stevenchadburrow/AcolyteHandheld/HandheldPIC32.kicad_sch

## KiCad design HandheldPIC32.kicad_sch (2025-06-16)

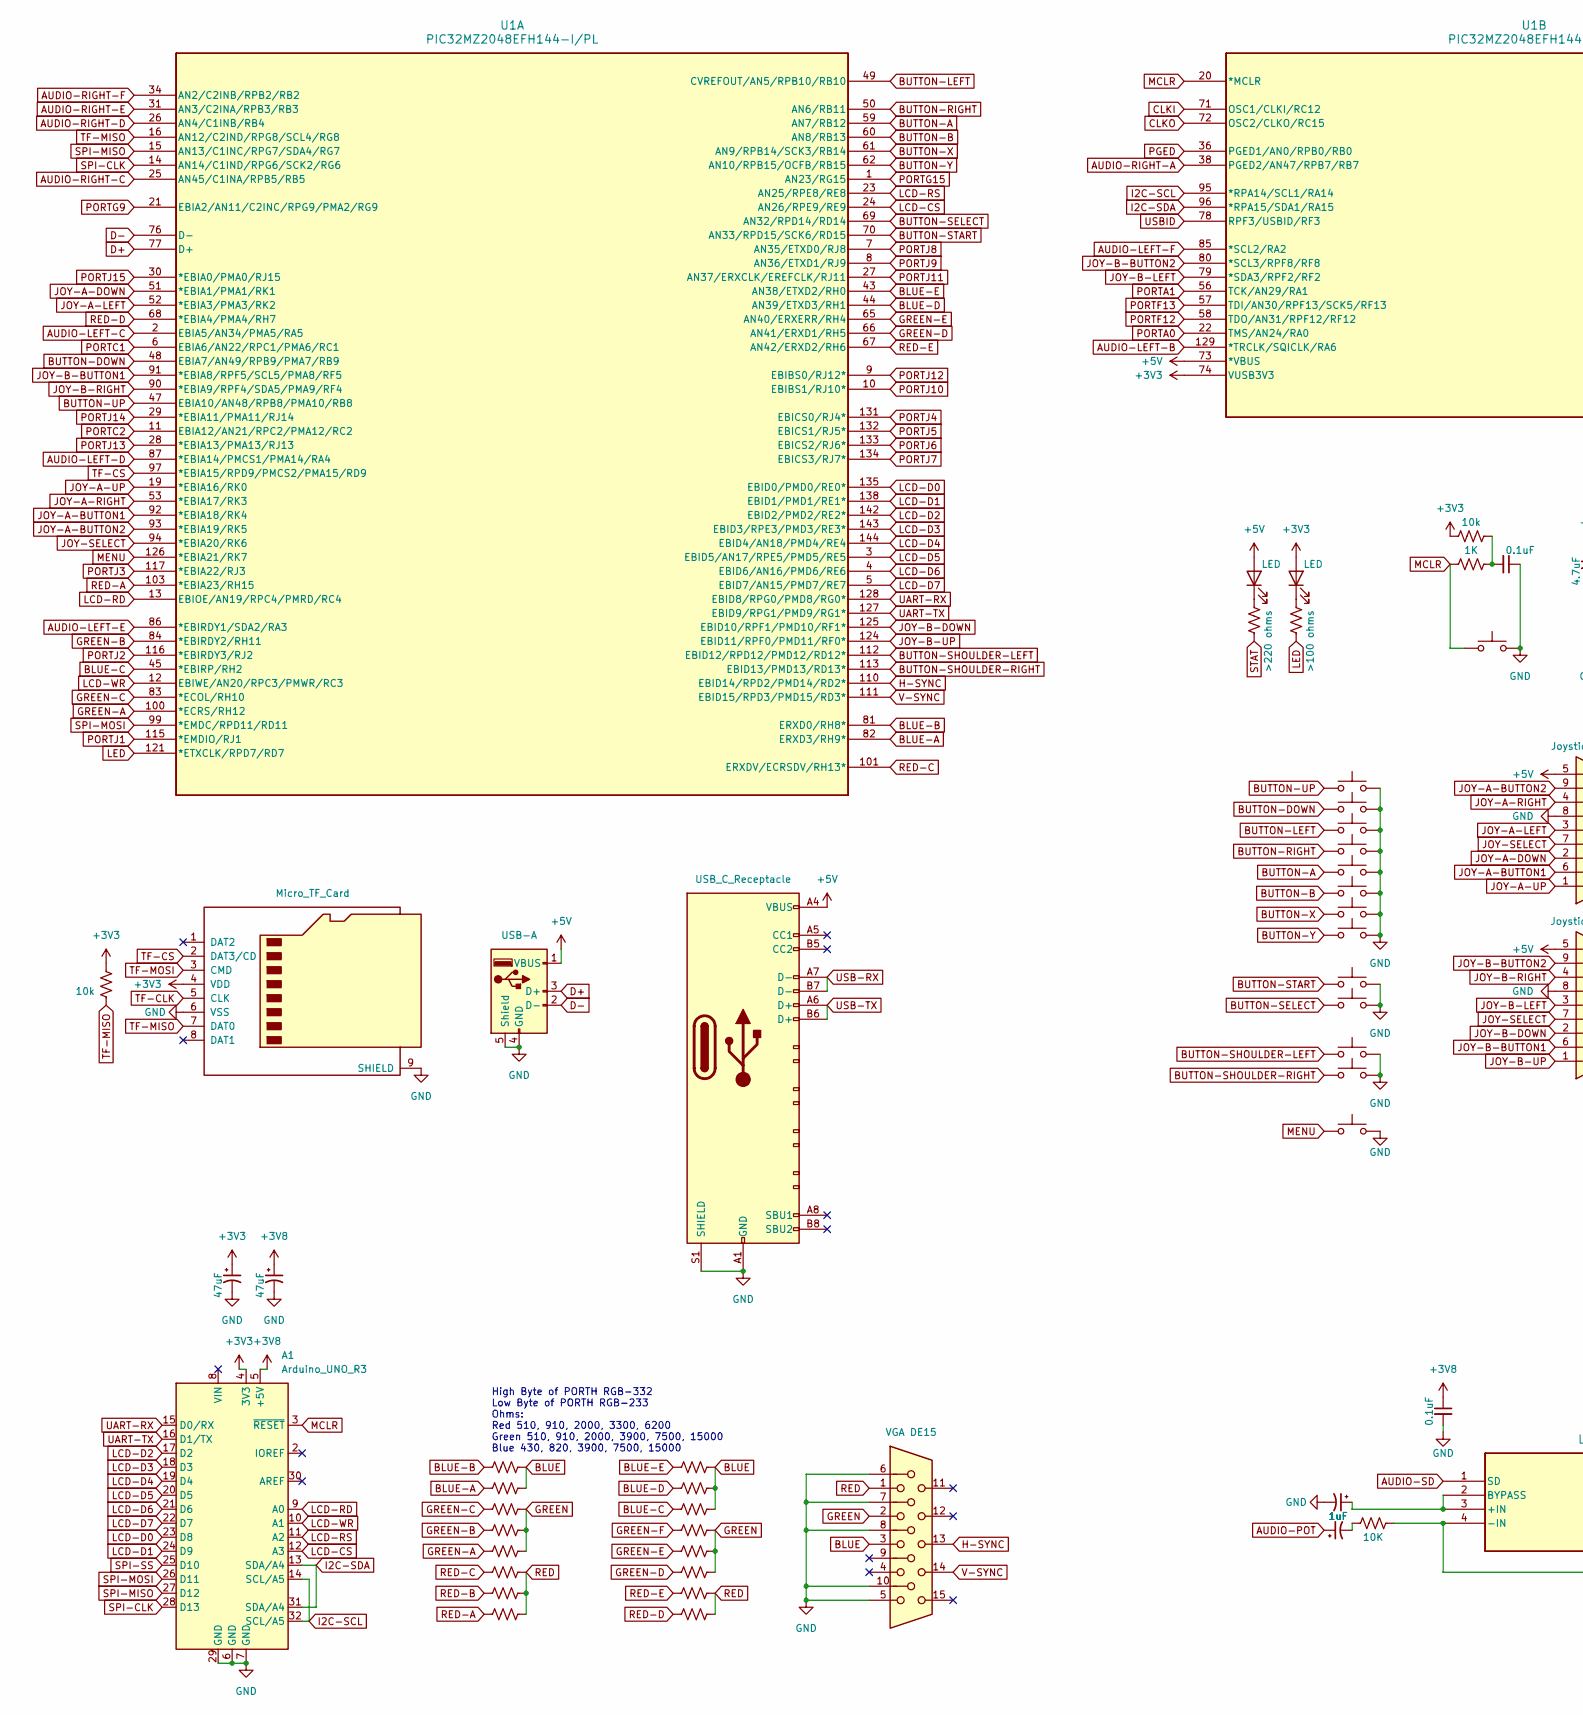
[picture p9: schematic HandheldPIC32.kicad_sch, part in row 1, column 1]

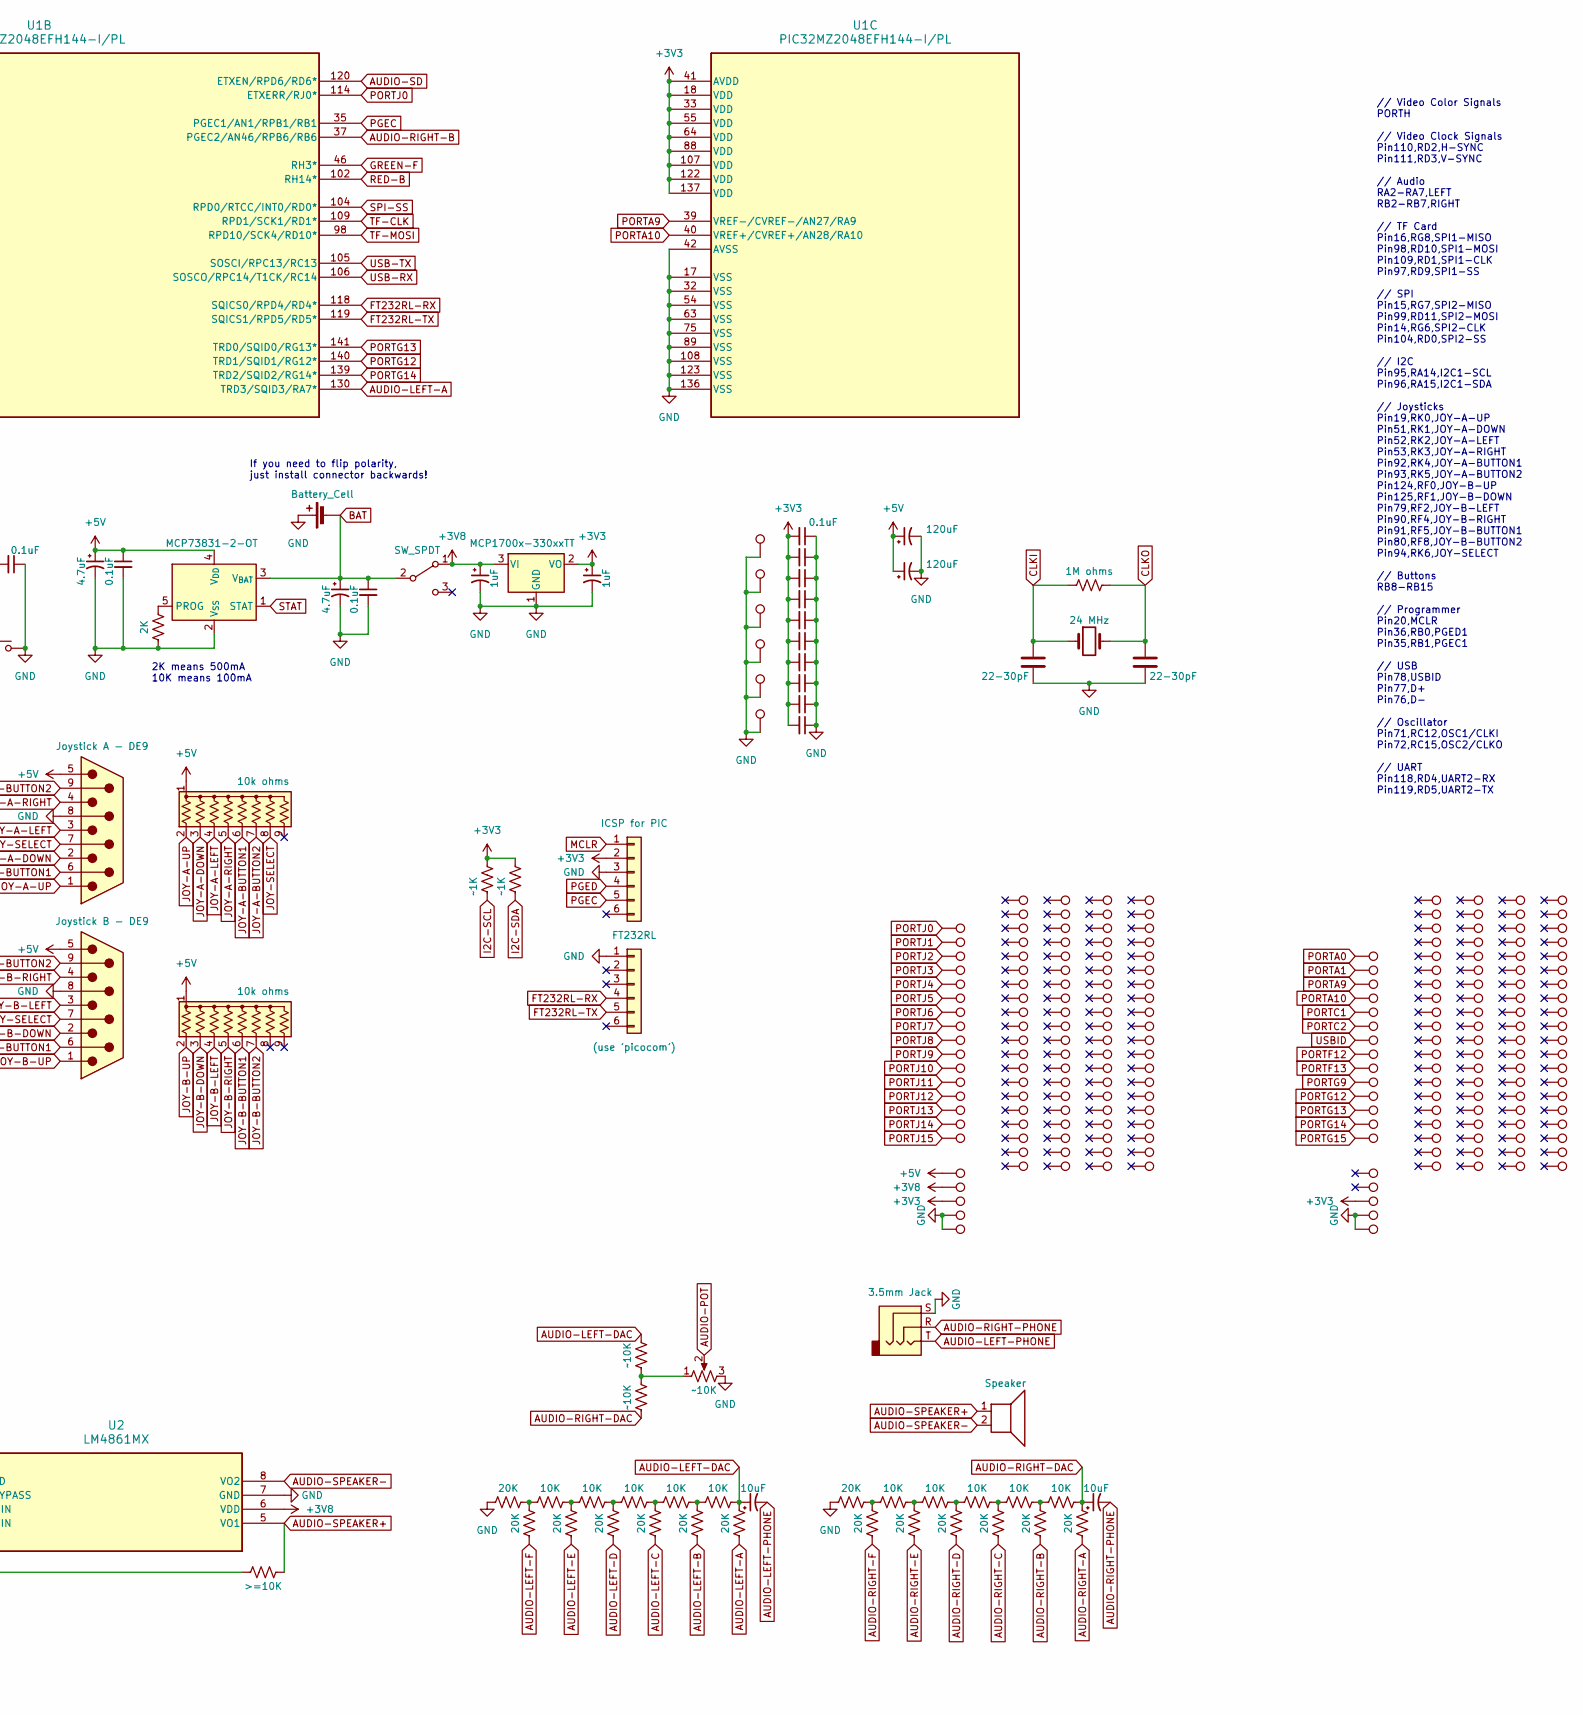
[picture p10: schematic HandheldPIC32.kicad_sch, part in row 1, column 2]

Parts:
A1: Arduino_UNO_R3; Arduino_UNO_R3-modified
BT1: Battery_Cell; JST_PH_B2B-PH-K_1x02_P2.00mm_Vertical
C1, C18, C19, C21, C22, C23, C24, C25, C26, C27: C_Polarized_Small_US; CP_Radial_D6.3mm_P2.50mm
C2, C3: C; C_Disc_D3.8mm_W2.6mm_P2.50mm
C4, C5, C6, C7, C8, C9, C10, C11, C12, C13, C14, C15, C20, C33: C_Small; C_Disc_D3.0mm_W1.6mm_P2.50mm
C16, C17: C_Polarized_Small_US; CP_Radial_D8.0mm_P3.50mm
D1, D3: LED; CustomLED
J1: DE15_Receptacle_HighDensity; DSUB-15-HD_Female_Horizontal_P2.29x2.54mm_VGA
J2: Conn_01x06; PinHeader_1x06_P2.54mm_Horizontal
J3: Conn_01x06; PinSocket_1x06_P2.54mm_Horizontal
J4: AudioJack3; BIGJack_3.5mm_Ledino_KB3SPRS_Horizontal
J6: USB_A; USB_A_Molex_67643_Horizontal
J8, J9: DE9_Plug; DSUB-9_Male_Horizontal_P2.77x2.84mm_EdgePinOffset7.70mm_Hou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
J10: USB_C_Receptacle; USB_C_Receptacle_GCT_USB4085
J11: Micro_TF_Card; microSD_HC_Hirose_DM3D-SF
LS1: Speaker; JST_PH_B2B-PH-K_1x02_P2.00mm_Vertical
R1, R2, R3, R4, R5, R6, R7, R8, R9, R10, R11, R12, R13, R14, R15, R16, R17, R18, R19, R20, R21, R22, R23, R24, R25, R26, R27, R28, R29, R30, R31, R32, R33, R34, R35, R36, R37, R38, R39, R40, R41, R42, R43, R44, R45, R46, R47, R48, R49, R50, R51, R53, R54: R_US; R_Axial_DIN0207_L6.3mm_D2.5mm_P10.16mm_Horizontal
RN1, RN2: R_Network08_US; R_Array_SIP9
RV1: R_Potentiometer_US; Potentiometer_Bourns_PTV09A-2_Single_Horizontal
SW1, SW2, SW3, SW5, SW6, SW7, SW8, SW9, SW10, SW11, SW12, SW15: SW_Push; SW_PUSH_6mm_H8mm
SW4: SW_SPDT; SW_E-Switch_EG1224_SPDT_Angled
SW14, SW16: SW_Push; SW_Tactile_SPST_Angled_PTS645Vx83-2LFS
TP1, TP2, TP3, TP4, TP6, TP7: TestPoint; ScrewHole-4-40
TP5, TP8, TP9, TP10, TP11, TP12, TP18, TP19, TP20, TP21, TP22, TP23, TP24, TP25, TP26, TP27, TP28, TP29, TP30, TP31, TP32, TP33, TP34, TP35, TP36, TP37, TP38, TP39, TP40, TP41, TP42, TP43, TP44, TP45, TP46, TP47, TP48, TP49, TP50, TP51, TP52, TP53, TP54, TP55, TP56, TP57, TP58, TP59, TP60, TP61, TP62, TP63, TP64, TP65, TP66, TP67, TP68, TP69, TP70, TP71, TP72, TP73, TP74, TP75, TP76, TP77, TP78, TP79, TP80, TP81, TP82, TP83, TP84, TP85, TP86, TP87, TP117, TP118, TP119, TP120, TP121, TP122, TP123, TP124, TP125, TP126, TP127, TP128, TP129, TP130, TP131, TP132, TP133, TP134, TP135, TP136, TP137, TP138, TP139, TP140, TP141, TP142, TP143, TP144, TP145, TP146, TP147, TP148, TP149, TP150, TP151, TP152, TP153, TP154, TP155, TP156, TP157, TP158, TP159, TP160, TP161, TP162, TP163, TP164, TP165, TP166, TP167, TP168, TP169, TP170, TP171, TP172, TP173, TP174, TP175, TP176, TP177, TP178, TP179, TP180, TP181, TP182, TP183, TP184, TP185, TP186, TP187, TP188, TP189, TP190, TP191, TP192, TP193, TP194, TP195, TP196, TP197, TP198, TP199, TP200, TP201, TP202, TP203, TP204, TP205, TP206, TP207, TP208, TP209, TP210: TestPoint; TestPointStdTHT
TP13, TP14, TP15, TP16, TP17, TP88, TP89, TP90, TP91, TP92, TP93, TP94, TP95, TP96, TP97, TP98, TP99, TP100, TP101, TP102, TP103, TP104, TP105, TP106, TP107, TP108, TP109, TP110, TP111, TP112: TestPoint; TestPoint_custom_THTPad_D1.5mm_Drill0.7mm
U1: PIC32MZ2048EFH144-I/PL; LQFP144_PL_MCH
U2: LM4861MX; SOIC-8_3.9x4.9mm_P1.27mm
U3: MCP73831-2-OT; SOT-23-5
U4: MCP1700x-330xxTT; SOT-23
Y1: Crystal; Crystal_HC49-4H_Vertical

Connections:
+3V3: A1.4 (3V3), C6.2, C7.2, C8.2, C9.2, C10.2, C11.2, C12.2, C13.2, C14.2, C15.2, C22.1, C23.1, D1.2 (A), J2.2, J11.4 (VDD), R21.2, R22.2, R35.1, R38.1, TP10.1, TP119.1, U1.18 (VDD), U1.33 (VDD), U1.41 (AVDD), U1.55 (VDD), U1.64 (VDD), U1.74 (VUSB3V3), U1.88 (VDD), U1.107 (VDD), U1.122 (VDD), U1.137 (VDD), U4.2 (VO)
+3V8: A1.5 (+5V), C1.1, C24.1, C33.1, SW4.1 (A), TP9.1, U2.6 (VDD), U4.3 (VI)
+5V: C16.1, C17.1, C20.1, C26.1, D3.2 (A), J6.1 (VBUS), J8.5, J9.5, J10.A4 (VBUS), J10.A9 (VBUS), J10.B4 (VBUS), J10.B9 (VBUS), RN1.1 (common), RN2.1 (common), TP8.1, U1.73 (*VBUS), U3.4 (V_{DD})
AUDIO-LEFT-A: R37.2, U1.130 (TRD3/SQID3/RA7*)
AUDIO-LEFT-B: R23.2, U1.129 (*TRCLK/SQICLK/RA6)
AUDIO-LEFT-C: R26.2, U1.2 (EBIA5/AN34/PMA5/RA5)
AUDIO-LEFT-D: R28.2, U1.87 (*EBIA14/PMCS1/PMA14/RA4)
AUDIO-LEFT-DAC: C21.1, R34.1, R37.1, R50.1
AUDIO-LEFT-E: R31.2, U1.86 (*EBIRDY1/SDA2/RA3)
AUDIO-LEFT-F: R32.2, U1.85 (*SCL2/RA2)
AUDIO-LEFT-PHONE: C21.2, J4.T
AUDIO-POT: C19.1, RV1.2
AUDIO-RIGHT-A: R49.2, U1.38 (PGED2/AN47/RPB7/RB7)
AUDIO-RIGHT-B: R47.2, U1.37 (PGEC2/AN46/RPB6/RB6)
AUDIO-RIGHT-C: R45.2, U1.25 (AN45/C1INA/RPB5/RB5)
AUDIO-RIGHT-D: R43.2, U1.26 (AN4/C1INB/RB4)
AUDIO-RIGHT-DAC: C27.1, R48.1, R49.1, R51.2
AUDIO-RIGHT-E: R41.2, U1.31 (AN3/C2INA/RPB3/RB3)
AUDIO-RIGHT-F: R39.2, U1.34 (AN2/C2INB/RPB2/RB2)
AUDIO-RIGHT-PHONE: C27.2, J4.R
AUDIO-SD: U1.120 (ETXEN/RPD6/RD6*), U2.1 (SD)
AUDIO-SPEAKER+: LS1.1, R54.2, U2.5 (VO1)
AUDIO-SPEAKER-: LS1.2, U2.8 (VO2)
BAT: BT1.2 (-), C4.1, C25.1, SW4.2 (B), U3.3 (V_{BAT})
BLUE: J1.3, R1.1, R2.1, R10.1, R11.1, R12.1
BLUE-A: R2.2, U1.82 (ERXD3/RH9*)
BLUE-B: R1.2, U1.81 (ERXD0/RH8*)
BLUE-C: R12.2, U1.45 (*EBIRP/RH2)
BLUE-D: R11.2, U1.44 (AN39/ETXD3/RH1)
BLUE-E: R10.2, U1.43 (AN38/ETXD2/RH0)
BUTTON-A: SW8.1, U1.59 (AN7/RB12)
BUTTON-B: SW9.1, U1.60 (AN8/RB13)
BUTTON-DOWN: SW5.1, U1.48 (EBIA7/AN49/RPB9/PMA7/RB9)
BUTTON-LEFT: SW6.1, U1.49 (CVREFOUT/AN5/RPB10/RB10)
BUTTON-RIGHT: SW7.1, U1.50 (AN6/RB11)
BUTTON-SELECT: SW2.1, U1.69 (AN32/RPD14/RD14)
BUTTON-SHOULDER-LEFT: SW14.1, U1.112 (EBID12/RPD12/PMD12/RD12*)
BUTTON-SHOULDER-RIGHT: SW16.1, U1.113 (EBID13/PMD13/RD13*)
BUTTON-START: SW1.1, U1.70 (AN33/RPD15/SCK6/RD15)
BUTTON-UP: SW3.1, U1.47 (EBIA10/AN48/RPB8/PMA10/RB8)
BUTTON-X: SW10.1, U1.61 (AN9/RPB14/SCK3/RB14)
BUTTON-Y: SW11.1, U1.62 (AN10/RPB15/OCFB/RB15)
CLKI: C2.1, R9.1, U1.71 (OSC1/CLKI/RC12), Y1.1
CLKO: C3.1, R9.2, U1.72 (OSC2/CLKO/RC15), Y1.2
D+: J6.3 (D+), U1.77 (D+)
D-: J6.2 (D-), U1.76 (D-)
FT232RL-RX: J3.4, U1.118 (SQICS0/RPD4/RD4*)
FT232RL-TX: J3.5, U1.119 (SQICS1/RPD5/RD5*)
GND: A1.6 (GND), A1.7 (GND), A1.29 (GND), BT1.1 (+), C1.2, C2.2, C3.2, C4.2, C5.1, C6.1, C7.1, C8.1, C9.1, C10.1, C11.1, C12.1, C13.1, C14.1, C15.1, C16.2, C17.2, C18.2, C20.2, C22.2, C23.2, C24.2, C25.2, C26.2, C33.2, J1.5, J1.6, J1.7, J1.8, J1.10, J2.3, J3.1, J4.S, J6.4 (GND), J6.5 (Shield), J8.8, J9.8, J10.A1 (GND), J10.A12 (GND), J10.B1 (GND), J10.B12 (GND), J10.S1 (SHIELD), J11.6 (VSS), J11.9 (SHIELD), R20.2, R30.2, R33.2, RV1.3, SW1.2, SW2.2, SW3.2, SW5.2, SW6.2, SW7.2, SW8.2, SW9.2, SW10.2, SW11.2, SW12.2, SW14.2, SW15.2, SW16.2, TP1.1, TP2.1, TP3.1, TP4.1, TP6.1, TP7.1, TP11.1, TP12.1, TP120.1, TP121.1, U1.17 (VSS), U1.32 (VSS), U1.42 (AVSS), U1.54 (VSS), U1.63 (VSS), U1.75 (VSS), U1.89 (VSS), U1.108 (VSS), U1.123 (VSS), U1.136 (VSS), U2.7 (GND), U3.2 (V_{SS}), U4.1 (GND)
GREEN: J1.2, R3.1, R4.1, R5.1, R13.1, R14.1, R15.1
GREEN-A: R5.2, U1.100 (*ECRS/RH12)
GREEN-B: R4.2, U1.84 (*EBIRDY2/RH11)
GREEN-C: R3.2, U1.83 (*ECOL/RH10)
GREEN-D: R15.2, U1.66 (AN41/ERXD1/RH5)
GREEN-E: R14.2, U1.65 (AN40/ERXERR/RH4)
GREEN-F: R13.2, U1.46 (RH3*)
H-SYNC: J1.13, U1.110 (EBID14/RPD2/PMD14/RD2*)
I2C-SCL: A1.14 (SCL/A5), A1.32 (SCL/A5), R35.2, U1.95 (*RPA14/SCL1/RA14)
I2C-SDA: A1.13 (SDA/A4), A1.31 (SDA/A4), R38.2, U1.96 (*RPA15/SDA1/RA15)
JOY-A-BUTTON1: J8.6, RN1.6 (R5), U1.92 (*EBIA18/RK4)
JOY-A-BUTTON2: J8.9, RN1.7 (R6), U1.93 (*EBIA19/RK5)
JOY-A-DOWN: J8.2, RN1.3 (R2), U1.51 (*EBIA1/PMA1/RK1)
JOY-A-LEFT: J8.3, RN1.4 (R3), U1.52 (*EBIA3/PMA3/RK2)
JOY-A-RIGHT: J8.4, RN1.5 (R4), U1.53 (*EBIA17/RK3)
JOY-A-UP: J8.1, RN1.2 (R1), U1.19 (*EBIA16/RK0)
JOY-B-BUTTON1: J9.6, RN2.6 (R5), U1.91 (*EBIA8/RPF5/SCL5/PMA8/RF5)
JOY-B-BUTTON2: J9.9, RN2.7 (R6), U1.80 (*SCL3/RPF8/RF8)
JOY-B-DOWN: J9.2, RN2.3 (R2), U1.125 (EBID10/RPF1/PMD10/RF1*)
JOY-B-LEFT: J9.3, RN2.4 (R3), U1.79 (*SDA3/RPF2/RF2)
JOY-B-RIGHT: J9.4, RN2.5 (R4), U1.90 (*EBIA9/RPF4/SDA5/PMA9/RF4)
JOY-B-UP: J9.1, RN2.2 (R1), U1.124 (EBID11/RPF0/PMD11/RF0*)
JOY-SELECT: J8.7, J9.7, RN1.8 (R7), U1.94 (*EBIA20/RK6)
LCD-CS: A1.12 (A3), U1.24 (AN26/RPE9/RE9)
LCD-D0: A1.23 (D8), U1.135 (EBID0/PMD0/RE0*)
LCD-D1: A1.24 (D9), U1.138 (EBID1/PMD1/RE1*)
LCD-D2: A1.17 (D2), U1.142 (EBID2/PMD2/RE2*)
LCD-D3: A1.18 (D3), U1.143 (EBID3/RPE3/PMD3/RE3*)
LCD-D4: A1.19 (D4), U1.144 (EBID4/AN18/PMD4/RE4)
LCD-D5: A1.20 (D5), U1.3 (EBID5/AN17/RPE5/PMD5/RE5)
LCD-D6: A1.21 (D6), U1.4 (EBID6/AN16/PMD6/RE6)
LCD-D7: A1.22 (D7), U1.5 (EBID7/AN15/PMD7/RE7)
LCD-RD: A1.9 (A0), U1.13 (EBIOE/AN19/RPC4/PMRD/RC4)
LCD-RS: A1.11 (A2), U1.23 (AN25/RPE8/RE8)
LCD-WR: A1.10 (A1), U1.12 (EBIWE/AN20/RPC3/PMWR/RC3)
LED: R25.2, U1.121 (*ETXCLK/RPD7/RD7)
MCLR: A1.3 (~RESET), J2.1, R18.2, SW15.1, U1.20 (*MCLR)
MENU: SW12.1, U1.126 (*EBIA21/RK7)
unnamed: C5.2, R18.1, R21.1
unnamed: C18.1, U2.2 (BYPASS), U2.3 (+IN)
unnamed: C19.2, R53.1
unnamed: D1.1 (K), R25.1
unnamed: D3.1 (K), R36.1
unnamed: R19.1, R24.2, R31.1
unnamed: R19.2, R32.1, R33.1
unnamed: R20.1, U3.5 (PROG)
unnamed: R23.1, R29.1, R34.2
unnamed: R24.1, R27.2, R28.1
unnamed: R26.1, R27.1, R29.2
unnamed: R30.1, R39.1, R40.2
unnamed: R40.1, R41.1, R42.2
unnamed: R42.1, R43.1, R44.2
unnamed: R44.1, R45.1, R46.2
unnamed: R46.1, R47.1, R48.2
unnamed: R50.2, R51.1, RV1.1
unnamed: R53.2, R54.1, U2.4 (-IN)
PGEC: J2.5, U1.35 (PGEC1/AN1/RPB1/RB1)
PGED: J2.4, U1.36 (PGED1/AN0/RPB0/RB0)
PORTA0: TP14.1, U1.22 (TMS/AN24/RA0)
PORTA1: TP13.1, U1.56 (TCK/AN29/RA1)
PORTA9: TP15.1, U1.39 (VREF-/CVREF-/AN27/RA9)
PORTA10: TP16.1, U1.40 (VREF+/CVREF+/AN28/RA10)
PORTC1: TP17.1, U1.6 (EBIA6/AN22/RPC1/PMA6/RC1)
PORTC2: TP88.1, U1.11 (EBIA12/AN21/RPC2/PMA12/RC2)
PORTF12: TP90.1, U1.58 (TDO/AN31/RPF12/RF12)
PORTF13: TP91.1, U1.57 (TDI/AN30/RPF13/SCK5/RF13)
PORTG9: TP108.1, U1.21 (EBIA2/AN11/C2INC/RPG9/PMA2/RG9)
PORTG12: TP109.1, U1.140 (TRD1/SQID1/RG12*)
PORTG13: TP110.1, U1.141 (TRD0/SQID0/RG13*)
PORTG14: TP111.1, U1.139 (TRD2/SQID2/RG14*)
PORTG15: TP112.1, U1.1 (AN23/RG15)
PORTJ0: TP92.1, U1.114 (ETXERR/RJ0*)
PORTJ1: TP93.1, U1.115 (*EMDIO/RJ1)
PORTJ2: TP94.1, U1.116 (*EBIRDY3/RJ2)
PORTJ3: TP95.1, U1.117 (*EBIA22/RJ3)
PORTJ4: TP96.1, U1.131 (EBICS0/RJ4*)
PORTJ5: TP97.1, U1.132 (EBICS1/RJ5*)
PORTJ6: TP98.1, U1.133 (EBICS2/RJ6*)
PORTJ7: TP99.1, U1.134 (EBICS3/RJ7*)
PORTJ8: TP100.1, U1.7 (AN35/ETXD0/RJ8)
PORTJ9: TP101.1, U1.8 (AN36/ETXD1/RJ9)
PORTJ10: TP102.1, U1.10 (EBIBS1/RJ10*)
PORTJ11: TP103.1, U1.27 (AN37/ERXCLK/EREFCLK/RJ11)
PORTJ12: TP104.1, U1.9 (EBIBS0/RJ12*)
PORTJ13: TP105.1, U1.28 (*EBIA13/PMA13/RJ13)
PORTJ14: TP106.1, U1.29 (*EBIA11/PMA11/RJ14)
PORTJ15: TP107.1, U1.30 (*EBIA0/PMA0/RJ15)
RED: J1.1, R6.1, R7.1, R8.1, R16.1, R17.1
RED-A: R8.2, U1.103 (*EBIA23/RH15)
RED-B: R7.2, U1.102 (RH14*)
RED-C: R6.2, U1.101 (ERXDV/ECRSDV/RH13*)
RED-D: R17.2, U1.68 (*EBIA4/PMA4/RH7)
RED-E: R16.2, U1.67 (AN42/ERXD2/RH6)
SPI-CLK: A1.28 (D13), U1.14 (AN14/C1IND/RPG6/SCK2/RG6)
SPI-MISO: A1.27 (D12), U1.15 (AN13/C1INC/RPG7/SDA4/RG7)
SPI-MOSI: A1.26 (D11), U1.99 (*EMDC/RPD11/RD11)
SPI-SS: A1.25 (D10), U1.104 (RPD0/RTCC/INT0/RD0*)
STAT: R36.2, U3.1 (STAT)
TF-CLK: J11.5 (CLK), U1.109 (RPD1/SCK1/RD1*)
TF-CS: J11.2 (DAT3/CD), U1.97 (*EBIA15/RPD9/PMCS2/PMA15/RD9)
TF-MISO: J11.7 (DAT0), R22.1, U1.16 (AN12/C2IND/RPG8/SCL4/RG8)
TF-MOSI: J11.3 (CMD), U1.98 (RPD10/SCK4/RD10*)
UART-RX: A1.15 (D0/RX), U1.128 (EBID8/RPG0/PMD8/RG0*)
UART-TX: A1.16 (D1/TX), U1.127 (EBID9/RPG1/PMD9/RG1*)
USB-RX: J10.A7 (D-), J10.B7 (D-), U1.106 (SOSCO/RPC14/T1CK/RC14)
USB-TX: J10.A6 (D+), J10.B6 (D+), U1.105 (SOSCI/RPC13/RC13)
USBID: TP89.1, U1.78 (RPF3/USBID/RF3)
V-SYNC: J1.14, U1.111 (EBID15/RPD3/PMD15/RD3*)

Notes on the sheet:
If you need to flip polarity, just install connector backwards!
// Video Color Signals PORTH // Video Clock Signals Pin110,RD2,H-SYNC Pin111,RD3,V-SYNC // Audio RA2-RA7,LEFT RB2-RB7,RIGHT // TF Card Pin16,RG8,SPI1-MISO Pin98,RD10,SPI1-MOSI Pin109,RD1,SPI1-CLK Pin97,RD9,SPI1-SS // SPI Pin15,RG7,SPI2-MISO Pin99,RD11,SPI2-MOSI Pin14,RG6,SPI2-CLK Pin104,RD0,SPI2-SS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
High Byte of PORTH RGB-332 Low Byte of PORTH RGB-233 Ohms: Red 510, 910, 2000, 3300, 6200 Green 510, 910, 2000, 3900, 7500, 15000 Blue 430, 820, 3900, 7500, 15000
2K means 500mA 10K means 100mA
