stevenchadburrow/AcolyteHandheld/peanut_gbc.h

/**
 * MIT License
 *
 * Copyright (c) 2018 Mahyar Koshkouei
 *
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
 * Please note that at least three parts of source code within this project was
 * taken from the SameBoy project at https://github.com/LIJI32/SameBoy/ which at
 * the time of this writing is released under the MIT License. Occurrences of
 * this code is marked as being taken from SameBoy with a comment.
 * SameBoy, and code marked as being taken from SameBoy,
 * is Copyright (c) 2015-2019 Lior Halphon.
 */

/*
 * THIS VERSION WAS COPIED FROM FROGGESTSPIRIT'S GITHUB REPO FOR GAMEBOY COLOR FUNCTIONALITY.
 * THIS IS STILL UNDER THE MIT LICENSE ABOVE.
 * https://github.com/froggestspirit/Peanut-GB
 */

#pragma once

volatile uint8_t __attribute__((coherent)) scanline_pixels1[160] = {0};
volatile uint8_t __attribute__((coherent)) scanline_pixels2[160] = {0};
volatile uint8_t __attribute__((coherent)) scanline_pixels_prio[160] = {0};  //do these pixels have priority over OAM?
volatile uint8_t scanline_scaled = 1; // default to 1.5x scale
volatile uint8_t scanline_toggle = 0;
volatile uint8_t scanline_count = 0;
volatile uint8_t scanline_draw = 0;
volatile uint8_t scanline_sync = 0;
volatile uint8_t scanline_hack = 1; // default on, removes sprite priority issues with GBC

#include <stdlib.h>	/* Required for qsort and abort */
#include <stdbool.h>	/* Required for bool types */
#include <stdint.h>	/* Required for int types */
#include <string.h>	/* Required for memset */
#include <time.h>	/* Required for tm struct */

/**
 * Sound support must be provided by an external library. When audio_read() and
 * audio_write() functions are provided, define ENABLE_SOUND to a non-zero value
 * before including peanut_gb.h in order for these functions to be used.
 */
#ifndef ENABLE_SOUND
#define ENABLE_SOUND 1
#endif

/* Enable LCD drawing. On by default. May be turned off for testing purposes. */
#ifndef ENABLE_LCD
#define ENABLE_LCD 1
#endif

/* Interrupt masks */
#define VBLANK_INTR 0x01
#define LCDC_INTR 0x02
#define TIMER_INTR 0x04
#define SERIAL_INTR 0x08
#define CONTROL_INTR 0x10
#define ANY_INTR 0x1F

/* Memory section sizes for DMG */
#define SRAM_SIZE 0x20000
#define WRAM_SIZE 0x8000
#define VRAM_SIZE 0x4000
#define HRAM_SIZE 0x0100
#define OAM_SIZE 0x00A0

/* Memory addresses */
#define ROM_0_ADDR 0x0000
#define ROM_N_ADDR 0x4000
#define VRAM_ADDR 0x8000
#define CART_RAM_ADDR 0xA000
#define WRAM_0_ADDR 0xC000
#define WRAM_1_ADDR 0xD000
#define ECHO_ADDR 0xE000
#define OAM_ADDR 0xFE00
#define UNUSED_ADDR 0xFEA0
#define IO_ADDR 0xFF00
#define HRAM_ADDR 0xFF80
#define INTR_EN_ADDR 0xFFFF

/* Cart section sizes */
#define ROM_BANK_SIZE 0x4000
#define WRAM_BANK_SIZE 0x1000
#define CRAM_BANK_SIZE 0x2000
#define VRAM_BANK_SIZE 0x2000

/* DIV Register is incremented at rate of 16384Hz.
 * 4194304 / 16384 = 256 clock cycles for one increment. */
#define DIV_CYCLES 256

/* Serial clock locked to 8192Hz on DMG.
 * 4194304 / (8192 / 8) = 4096 clock cycles for sending 1 byte. */
#define SERIAL_CYCLES 4096

/* Calculating VSYNC. */
#define DMG_CLOCK_FREQ 4194304.0
#define SCREEN_REFRESH_CYCLES 70224.0
#define VERTICAL_SYNC (DMG_CLOCK_FREQ / SCREEN_REFRESH_CYCLES)

/* SERIAL SC register masks. */
#define SERIAL_SC_TX_START 0x80
#define SERIAL_SC_CLOCK_SRC 0x01

/* STAT register masks */
#define STAT_LYC_INTR 0x40
#define STAT_MODE_2_INTR 0x20
#define STAT_MODE_1_INTR 0x10
#define STAT_MODE_0_INTR 0x08
#define STAT_LYC_COINC 0x04
#define STAT_MODE 0x03
#define STAT_USER_BITS 0xF8

/* LCDC control masks */
#define LCDC_ENABLE 0x80
#define LCDC_WINDOW_MAP 0x40
#define LCDC_WINDOW_ENABLE 0x20
#define LCDC_TILE_SELECT 0x10
#define LCDC_BG_MAP 0x08
#define LCDC_OBJ_SIZE 0x04
#define LCDC_OBJ_ENABLE 0x02
#define LCDC_BG_ENABLE 0x01

/* LCD characteristics */
#define LCD_LINE_CYCLES 456
#define LCD_MODE_0_CYCLES 0
#define LCD_MODE_2_CYCLES 204
#define LCD_MODE_3_CYCLES 284
#define LCD_VERT_LINES 154
#define LCD_WIDTH 160
#define LCD_HEIGHT 144

/* VRAM Locations */
#define VRAM_TILES_1 (0x8000 - VRAM_ADDR)
#define VRAM_TILES_2 (0x8800 - VRAM_ADDR)
#define VRAM_BMAP_1 (0x9800 - VRAM_ADDR)
#define VRAM_BMAP_2 (0x9C00 - VRAM_ADDR)
#define VRAM_TILES_3 (0x8000 - VRAM_ADDR + VRAM_BANK_SIZE)
#define VRAM_TILES_4 (0x8800 - VRAM_ADDR + VRAM_BANK_SIZE)

/* Interrupt jump addresses */
#define VBLANK_INTR_ADDR 0x0040
#define LCDC_INTR_ADDR 0x0048
#define TIMER_INTR_ADDR 0x0050
#define SERIAL_INTR_ADDR 0x0058
#define CONTROL_INTR_ADDR 0x0060

/* SPRITE controls */
#define NUM_SPRITES 0x28
#define MAX_SPRITES_LINE 0x0A
#define OBJ_PRIORITY 0x80
#define OBJ_FLIP_Y 0x40
#define OBJ_FLIP_X 0x20
#define OBJ_PALETTE 0x10
#define OBJ_BANK 0x08
#define OBJ_CGB_PALETTE 0x07

/* Joypad buttons */
#define JOYPAD_A            0x01
#define JOYPAD_B            0x02
#define JOYPAD_SELECT       0x04
#define JOYPAD_START        0x08
#define JOYPAD_RIGHT        0x10
#define JOYPAD_LEFT         0x20
#define JOYPAD_UP           0x40
#define JOYPAD_DOWN         0x80

#define ROM_HEADER_CHECKSUM_LOC 0x014D

#ifndef MIN
#define MIN(a, b) ((a) < (b) ? (a) : (b))
#endif

struct cpu_registers_s {
    /* Combine A and F registers. */
    union {
        struct
        {
            /* Define specific bits of Flag register. */
            union {
                struct
                {
                    uint8_t unused : 4;
                    uint8_t c : 1; /* Carry flag. */
                    uint8_t h : 1; /* Half carry flag. */
                    uint8_t n : 1; /* Add/sub flag. */
                    uint8_t z : 1; /* Zero flag. */
                } f_bits;
                uint8_t f;
            };
            uint8_t a;
        };
        uint16_t af;
    };

    union {
        struct
        {
            uint8_t c;
            uint8_t b;
        };
        uint16_t bc;
    };

    union {
        struct
        {
            uint8_t e;
            uint8_t d;
        };
        uint16_t de;
    };

    union {
        struct
        {
            uint8_t l;
            uint8_t h;
        };
        uint16_t hl;
    };

    uint16_t sp; /* Stack pointer */
    uint16_t pc; /* Program counter */
};

struct count_s {
    uint_fast16_t lcd_count;    /* LCD Timing */
    uint_fast16_t div_count;    /* Divider Register Counter */
    uint_fast16_t tima_count;   /* Timer Counter */
    uint_fast16_t serial_count; /* Serial Counter */
};

struct gb_registers_s {
    /* TODO: Sort variables in address order. */
    /* Timing */
    uint8_t TIMA, TMA, DIV;
    union {
        struct
        {
            uint8_t tac_rate : 2;   /* Input clock select */
            uint8_t tac_enable : 1; /* Timer enable */
            uint8_t unused : 5;
        };
        uint8_t TAC;
    };

    /* LCD */
    uint8_t LCDC;
    uint8_t STAT;
    uint8_t SCY;
    uint8_t SCX;
    uint8_t LY;
    uint8_t LYC;
    uint8_t DMA;
    uint8_t BGP;
    uint8_t OBP0;
    uint8_t OBP1;
    uint8_t WY;
    uint8_t WX;

    /* Joypad info. */
    uint8_t P1;

    /* Serial data. */
    uint8_t SB;
    uint8_t SC;

    /* Interrupt flag. */
    uint8_t IF;

    /* Interrupt enable. */
    uint8_t IE;
};

#if ENABLE_LCD
/* Bit mask for the shade of pixel to display */
#define LCD_COLOUR 0x03
/**
    * Bit mask for whether a pixel is OBJ0, OBJ1, or BG. Each may have a different
    * palette when playing a DMG game on CGB.
    */
#define LCD_PALETTE_OBJ 0x10
#define LCD_PALETTE_BG 0x20
/**
    * Bit mask for the two bits listed above.
    * LCD_PALETTE_ALL == 0b00 --> OBJ0
    * LCD_PALETTE_ALL == 0b01 --> OBJ1
    * LCD_PALETTE_ALL == 0b10 --> BG
    * LCD_PALETTE_ALL == 0b11 --> NOT POSSIBLE
    */
#define LCD_PALETTE_ALL 0x30
#endif

/**
 * Errors that may occur during emulation.
 */
enum gb_error_e {
    GB_UNKNOWN_ERROR,
    GB_INVALID_OPCODE,
    GB_INVALID_READ,
    GB_INVALID_WRITE,

    GB_INVALID_MAX
};

/**
 * Errors that may occur during library initialisation.
 */
enum gb_init_error_e {
    GB_INIT_NO_ERROR,
    GB_INIT_CARTRIDGE_UNSUPPORTED,
    GB_INIT_INVALID_CHECKSUM
};

/**
 * Return codes for serial receive function, mainly for clarity.
 */
enum gb_serial_rx_ret_e {
    GB_SERIAL_RX_SUCCESS = 0,
    GB_SERIAL_RX_NO_CONNECTION = 1
};

/**
 * Emulator context.
 *
 * Only values within the `direct` struct may be modified directly by the
 * front-end implementation. Other variables must not be modified.
 */
struct gb_s {
    /**
     * Return byte from ROM at given address.
     *
     * \param gb_s    emulator context
     * \param addr    address
     * \return        byte at address in ROM
     */
    uint8_t (*gb_rom_read)(struct gb_s *, const uint_fast32_t addr);

    /**
     * Return byte from cart RAM at given address.
     *
     * \param gb_s    emulator context
     * \param addr    address
     * \return        byte at address in RAM
     */
    uint8_t (*gb_cart_ram_read)(struct gb_s *, const uint_fast32_t addr);

    /**
     * Write byte to cart RAM at given address.
     *
     * \param gb_s    emulator context
     * \param addr    address
     * \param val    value to write to address in RAM
     */
    void (*gb_cart_ram_write)(struct gb_s *, const uint_fast32_t addr,
                              const uint8_t val);

    /**
     * Notify front-end of error.
     *
     * \param gb_s            emulator context
     * \param gb_error_e    error code
     * \param val            arbitrary value related to error
     */
    void (*gb_error)(struct gb_s *, const enum gb_error_e, const uint16_t val);

    /* Transmit one byte and return the received byte. */
    void (*gb_serial_tx)(struct gb_s *, const uint8_t tx);
    enum gb_serial_rx_ret_e (*gb_serial_rx)(struct gb_s *, uint8_t *rx);

    /* Read byte from boot ROM at given address. */
	uint8_t (*gb_boot_rom_read)(struct gb_s*, const uint_fast16_t addr);
    
    struct
    {
        uint8_t gb_halt : 1;
        uint8_t gb_ime : 1;
        uint8_t gb_bios_enable : 1;
        uint8_t gb_frame : 1; /* New frame drawn. */

#define LCD_HBLANK 0
#define LCD_VBLANK 1
#define LCD_SEARCH_OAM 2
#define LCD_TRANSFER 3
        uint8_t lcd_mode : 2;
        uint8_t lcd_blank : 1;
    };

    /* Cartridge information:
     * Memory Bank Controller (MBC) type. */
    uint8_t mbc;
    /* Whether the MBC has internal RAM. */
    uint8_t cart_ram;
    /* Number of ROM banks in cartridge. */
    uint16_t num_rom_banks_mask;
    /* Number of RAM banks in cartridge. */
    uint8_t num_ram_banks;

    uint16_t selected_rom_bank;
    /* WRAM and VRAM bank selection not available. */
    uint8_t cart_ram_bank;
    uint16_t cart_ram_bank_offset;  //offset to subtract from the address to point to the right SRAM bank
    uint8_t enable_cart_ram;
    /* Cartridge ROM/RAM mode select. */
    uint8_t cart_mode_select;
    union {
        struct
        {
            uint8_t sec;
            uint8_t min;
            uint8_t hour;
            uint8_t yday;
            uint8_t high;
        } rtc_bits;
        uint8_t cart_rtc[5];
    };

    struct cpu_registers_s cpu_reg;
    struct gb_registers_s gb_reg;
    struct count_s counter;

    /* TODO: Allow implementation to allocate WRAM, VRAM and Frame Buffer. */
    volatile uint8_t __attribute__((coherent)) wram[WRAM_SIZE];
    volatile uint8_t __attribute__((coherent)) vram[VRAM_SIZE];
    volatile uint8_t __attribute__((coherent)) hram[HRAM_SIZE];
    volatile uint8_t __attribute__((coherent)) oam[OAM_SIZE];

    struct
    {
        /**
         * Draw line on screen.
         *
         * \param gb_s        emulator context
         * \param pixels    The 160 pixels to draw.
         *             Bits 1-0 are the colour to draw.
         *             Bits 5-4 are the palette, where:
         *                 OBJ0 = 0b00,
         *                 OBJ1 = 0b01,
         *                 BG = 0b10
         *             Other bits are undefined.
         *             Bits 5-4 are only required by front-ends
         *             which want to use a different colour for
         *             different object palettes. This is what
         *             the Game Boy Color (CGB) does to DMG
         *             games.
         * \param line        Line to draw pixels on. This is
         * guaranteed to be between 0-144 inclusive.
         */
        void (*lcd_draw_line)(struct gb_s *gb,
                              //const uint8_t *pixels,
                              const uint_fast8_t line);

        /* Palettes */
        uint8_t bg_palette[4];
        uint8_t sp_palette[8];

        uint8_t window_clear;
        uint8_t WY;

        /* Only support 30fps frame skip. */
        uint8_t frame_skip_count : 1;
        uint8_t interlace_count : 1;
    } display;

    /* Game Boy Color Mode*/
    struct {
        uint8_t cgbMode;
        uint8_t doubleSpeed;
        uint8_t doubleSpeedPrep;
        uint8_t wramBank;
        uint16_t wramBankOffset;
        uint8_t vramBank;
        uint16_t vramBankOffset;
        uint16_t fixPalette[0x40];  //BG then OAM palettes fixed for the screen
        uint8_t OAMPalette[0x40];
        uint8_t BGPalette[0x40];
        uint8_t OAMPaletteID;
        uint8_t BGPaletteID;
        uint8_t OAMPaletteInc;
        uint8_t BGPaletteInc;
        uint8_t dmaActive;
        uint8_t dmaMode;
        uint8_t dmaSize;
        uint16_t dmaSource;
        uint16_t dmaDest;
    } cgb;
    /**
     * Variables that may be modified directly by the front-end.
     * This method seems to be easier and possibly less overhead than
     * calling a function to modify these variables each time.
     *
     * None of this is thread-safe.
     */
    struct
    {
        /* Set to enable interlacing. Interlacing will start immediately
         * (at the next line drawing).
         */
        uint8_t interlace : 1;
        uint8_t frame_skip : 1;

        union {
            struct
            {
                uint8_t a : 1;
                uint8_t b : 1;
                uint8_t select : 1;
                uint8_t start : 1;
                uint8_t right : 1;
                uint8_t left : 1;
                uint8_t up : 1;
                uint8_t down : 1;
            } joypad_bits;
            uint8_t joypad;
        };

        /* Implementation defined data. Set to NULL if not required. */
        void *priv;
    } direct;
};

/**
 * Tick the internal RTC by one second.
 * This was taken from SameBoy, which is released under MIT Licence.
 */
void gb_tick_rtc(struct gb_s *gb) {
    /* is timer running? */
    if ((gb->cart_rtc[4] & 0x40) == 0) {
        if (++gb->rtc_bits.sec == 60) {
            gb->rtc_bits.sec = 0;

            if (++gb->rtc_bits.min == 60) {
                gb->rtc_bits.min = 0;

                if (++gb->rtc_bits.hour == 24) {
                    gb->rtc_bits.hour = 0;

                    if (++gb->rtc_bits.yday == 0) {
                        if (gb->rtc_bits.high & 1) /* Bit 8 of days*/
                        {
                            gb->rtc_bits.high |= 0x80; /* Overflow bit */
                        }

                        gb->rtc_bits.high ^= 1;
                    }
                }
            }
        }
    }
}

/**
 * Set initial values in RTC.
 * Should be called after gb_init().
 */
void gb_set_rtc(struct gb_s *gb, const struct tm *const time) {
    gb->cart_rtc[0] = time->tm_sec;
    gb->cart_rtc[1] = time->tm_min;
    gb->cart_rtc[2] = time->tm_hour;
    gb->cart_rtc[3] = time->tm_yday & 0xFF; /* Low 8 bits of day counter. */
    gb->cart_rtc[4] = time->tm_yday >> 8;   /* High 1 bit of day counter. */
}

/**
 * Internal function used to read bytes.
 */
uint8_t __gb_read(struct gb_s *gb, const uint_fast16_t addr) {
    switch (addr >> 12) {
        case 0x0:

        /* TODO: BIOS support. */
        case 0x1:
        case 0x2:
        case 0x3:
            return gb->gb_rom_read(gb, addr);

        case 0x4:
        case 0x5:
        case 0x6:
        case 0x7:
            if (gb->mbc == 1 && gb->cart_mode_select)
                return gb->gb_rom_read(gb,
                                       addr + ((gb->selected_rom_bank & 0x1F) - 1) * ROM_BANK_SIZE);
            else
                return gb->gb_rom_read(gb, addr + (gb->selected_rom_bank - 1) * ROM_BANK_SIZE);

        case 0x8:
        case 0x9:
            return gb->vram[addr - gb->cgb.vramBankOffset];

        case 0xA:
        case 0xB:
            if (gb->cart_ram && gb->enable_cart_ram) {
                if (gb->mbc == 3 && gb->cart_ram_bank >= 0x08)
                    return gb->cart_rtc[gb->cart_ram_bank - 0x08];
                else
                    return gb->gb_cart_ram_read(gb, addr - gb->cart_ram_bank_offset);
            }

            return 0xFF;

        case 0xC:
            return gb->wram[addr - WRAM_0_ADDR];

        case 0xD:
            return gb->wram[addr - gb->cgb.wramBankOffset];

        case 0xE:
            return gb->wram[addr - ECHO_ADDR];

        case 0xF:
            if (addr < OAM_ADDR)
                return gb->wram[(addr - 0x2000) - gb->cgb.wramBankOffset];

            if (addr < UNUSED_ADDR)
                return gb->oam[addr - OAM_ADDR];

            /* Unusable memory area. Reading from this area returns 0.*/
            if (addr < IO_ADDR)
                return 0xFF;

            /* HRAM */
            if (HRAM_ADDR <= addr && addr < INTR_EN_ADDR)
                return gb->hram[addr - IO_ADDR];

            if ((addr >= 0xFF10) && (addr <= 0xFF3F)) {
#if ENABLE_SOUND
                return audio_read_value(addr);
#else
                return 1;
#endif
            }

            /* IO and Interrupts. */
            switch (addr & 0xFF) {
                /* IO Registers */
                case 0x00:
                    return 0xC0 | gb->gb_reg.P1;

                case 0x01:
                    return gb->gb_reg.SB;

                case 0x02:
                    return gb->gb_reg.SC;

                /* Timer Registers */
                case 0x04:
                    return gb->gb_reg.DIV;

                case 0x05:
                    return gb->gb_reg.TIMA;

                case 0x06:
                    return gb->gb_reg.TMA;

                case 0x07:
                    return gb->gb_reg.TAC;

                /* Interrupt Flag Register */
                case 0x0F:
                    return gb->gb_reg.IF;

                /* LCD Registers */
                case 0x40:
                    return gb->gb_reg.LCDC;

                case 0x41:
                    return (gb->gb_reg.STAT & STAT_USER_BITS) |
                           (gb->gb_reg.LCDC & LCDC_ENABLE ? gb->lcd_mode : LCD_VBLANK);

                case 0x42:
                    return gb->gb_reg.SCY;

                case 0x43:
                    return gb->gb_reg.SCX;

                case 0x44:
                    return gb->gb_reg.LY;

                case 0x45:
                    return gb->gb_reg.LYC;

                /* DMA Register */
                case 0x46:
                    return gb->gb_reg.DMA;

                /* DMG Palette Registers */
                case 0x47:
                    return gb->gb_reg.BGP;

                case 0x48:
                    return gb->gb_reg.OBP0;

                case 0x49:
                    return gb->gb_reg.OBP1;

                /* Window Position Registers */
                case 0x4A:
                    return gb->gb_reg.WY;

                case 0x4B:
                    return gb->gb_reg.WX;

                /* Speed Switch*/
                case 0x4D:
                    return (gb->cgb.doubleSpeed << 7) + gb->cgb.doubleSpeedPrep;

                /* CGB VRAM Bank*/
                case 0x4F:
                    return gb->cgb.vramBank | 0xFE;

                /* CGB DMA*/
                case 0x51:
                    return (gb->cgb.dmaSource >> 8);
                case 0x52:
                    return (gb->cgb.dmaSource & 0xF0);
                case 0x53:
                    return (gb->cgb.dmaDest >> 8);
                case 0x54:
                    return (gb->cgb.dmaDest & 0xF0);
                case 0x55:
                    return (gb->cgb.dmaActive << 7) | (gb->cgb.dmaSize - 1);

                /* IR Register*/
                case 0x56:
                    return gb->hram[0x56];

                /* CGB BG Palette Index*/
                case 0x68:
                    return (gb->cgb.BGPaletteID & 0x3F) + (gb->cgb.BGPaletteInc << 7);

                /* CGB BG Palette*/
                case 0x69:
                    return gb->cgb.BGPalette[(gb->cgb.BGPaletteID & 0x3F)];

                /* CGB OAM Palette Index*/
                case 0x6A:
                    return (gb->cgb.OAMPaletteID & 0x3F) + (gb->cgb.OAMPaletteInc << 7);

                /* CGB OAM Palette*/
                case 0x6B:
                    return gb->cgb.OAMPalette[(gb->cgb.OAMPaletteID & 0x3F)];

                /* CGB WRAM Bank*/
                case 0x70:
                    return gb->cgb.wramBank;

                /* Interrupt Enable Register */
                case 0xFF:
                    return gb->gb_reg.IE;

                /* Unused registers return 1 */
                default:
                    return 0xFF;
            }
    }

    (gb->gb_error)(gb, GB_INVALID_READ, addr);
    return 0xFF;
}

/**
 * Internal function used to write bytes.
 */
void __gb_write(struct gb_s *gb, const uint_fast16_t addr, const uint8_t val) {
    switch (addr >> 12) {
        case 0x0:
        case 0x1:
            if (gb->mbc == 2 && addr & 0x10)
                return;
            else if (gb->mbc > 0 && gb->cart_ram)
                gb->enable_cart_ram = ((val & 0x0F) == 0x0A);

            return;

        case 0x2:
            if (gb->mbc == 5) {
                gb->selected_rom_bank = (gb->selected_rom_bank & 0x100) | val;
                gb->selected_rom_bank =
                    gb->selected_rom_bank & gb->num_rom_banks_mask;
                return;
            }

            /* Intentional fall through. */

        case 0x3:
            if (gb->mbc == 1) {
                //selected_rom_bank = val & 0x7;
                gb->selected_rom_bank = (val & 0x1F) | (gb->selected_rom_bank & 0x60);

                if ((gb->selected_rom_bank & 0x1F) == 0x00)
                    gb->selected_rom_bank++;
            } else if (gb->mbc == 2 && addr & 0x10) {
                gb->selected_rom_bank = val & 0x0F;

                if (!gb->selected_rom_bank)
                    gb->selected_rom_bank++;
            } else if (gb->mbc == 3) {
                gb->selected_rom_bank = val & 0x7F;

                if (!gb->selected_rom_bank)
                    gb->selected_rom_bank++;
            } else if (gb->mbc == 5)
                gb->selected_rom_bank = (val & 0x01) << 8 | (gb->selected_rom_bank & 0xFF);

            gb->selected_rom_bank = gb->selected_rom_bank & gb->num_rom_banks_mask;
            return;

        case 0x4:
        case 0x5:
            if (gb->mbc == 1) {
                gb->cart_ram_bank = (val & 3);
                gb->cart_ram_bank_offset = 0xA000 - (gb->cart_ram_bank << 13);
                gb->selected_rom_bank = ((val & 3) << 5) | (gb->selected_rom_bank & 0x1F);
                gb->selected_rom_bank = gb->selected_rom_bank & gb->num_rom_banks_mask;
            } else if (gb->mbc == 3) {
                gb->cart_ram_bank = val;
                gb->cart_ram_bank_offset = 0xA000 - ((gb->cart_ram_bank & 3) << 13);
            } else if (gb->mbc == 5) {
                gb->cart_ram_bank = (val & 0x0F);
                gb->cart_ram_bank_offset = 0xA000 - (gb->cart_ram_bank << 13);
            }
            return;

        case 0x6:
        case 0x7:
            gb->cart_mode_select = (val & 1);
            return;

        case 0x8:
        case 0x9:
            gb->vram[addr - gb->cgb.vramBankOffset] = val;
            return;

        case 0xA:
        case 0xB:
            if (gb->cart_ram && gb->enable_cart_ram) {
                if (gb->mbc == 3 && gb->cart_ram_bank >= 0x08)
                    gb->cart_rtc[gb->cart_ram_bank - 0x08] = val;
                else if (gb->num_ram_banks)
                    gb->gb_cart_ram_write(gb, addr - gb->cart_ram_bank_offset, val);
            }

            return;

        case 0xC:
            gb->wram[addr - WRAM_0_ADDR] = val;
            return;

        case 0xD:
            gb->wram[addr - gb->cgb.wramBankOffset] = val;
            return;

        case 0xE:
            gb->wram[addr - ECHO_ADDR] = val;
            return;

        case 0xF:
            if (addr < OAM_ADDR) {
                gb->wram[(addr - 0x2000) - gb->cgb.wramBankOffset] = val;
                return;
            }

            if (addr < UNUSED_ADDR) {
                gb->oam[addr - OAM_ADDR] = val;
                return;
            }

            /* Unusable memory area. */
            if (addr < IO_ADDR)
                return;

            if (HRAM_ADDR <= addr && addr < INTR_EN_ADDR) {
                gb->hram[addr - IO_ADDR] = val;
                return;
            }

            if ((addr >= 0xFF10) && (addr <= 0xFF3F)) {
#if ENABLE_SOUND
                audio_write_value(addr, val);
#endif
                return;
            }
            uint16_t fixPaletteTemp;
            /* IO and Interrupts. */
            switch (addr & 0xFF) {
                /* Joypad */
                case 0x00:
                    /* Only bits 5 and 4 are R/W.
             * The lower bits are overwritten later, and the two most
             * significant bits are unused. */
                    gb->gb_reg.P1 = val;

                    /* Direction keys selected */
                    if ((gb->gb_reg.P1 & 0b010000) == 0)
                        gb->gb_reg.P1 |= (gb->direct.joypad >> 4);
                    /* Button keys selected */
                    else
                        gb->gb_reg.P1 |= (gb->direct.joypad & 0x0F);

                    return;

                /* Serial */
                case 0x01:
                    gb->gb_reg.SB = val;
                    return;

                case 0x02:
                    gb->gb_reg.SC = val;
                    return;

                /* Timer Registers */
                case 0x04:
                    gb->gb_reg.DIV = 0x00;
                    return;

                case 0x05:
                    gb->gb_reg.TIMA = val;
                    return;

                case 0x06:
                    gb->gb_reg.TMA = val;
                    return;

                case 0x07:
                    gb->gb_reg.TAC = val;
                    return;

                /* Interrupt Flag Register */
                case 0x0F:
                    gb->gb_reg.IF = (val | 0b11100000);
                    return;

                /* LCD Registers */
                case 0x40:
                    if (((gb->gb_reg.LCDC & LCDC_ENABLE) == 0) &&
                        (val & LCDC_ENABLE)) {
                        gb->counter.lcd_count = 0;
                        gb->lcd_blank = 1;
                    }

                    gb->gb_reg.LCDC = val;

                    /* LY fixed to 0 when LCD turned off. */
                    if ((gb->gb_reg.LCDC & LCDC_ENABLE) == 0) {
                        /* Do not turn off LCD outside of VBLANK. This may
                 * happen due to poor timing in this emulator. */
                        if (gb->lcd_mode != LCD_VBLANK) {
                            gb->gb_reg.LCDC |= LCDC_ENABLE;
                            return;
                        }

                        gb->gb_reg.STAT = (gb->gb_reg.STAT & ~0x03) | LCD_VBLANK;
                        gb->gb_reg.LY = 0;
                        gb->counter.lcd_count = 0;
                    }

                    return;

                case 0x41:
                    gb->gb_reg.STAT = (val & 0b01111000);
                    return;

                case 0x42:
                    gb->gb_reg.SCY = val;
                    return;

                case 0x43:
                    gb->gb_reg.SCX = val;
                    return;

                /* LY (0xFF44) is read only. */
                case 0x45:
                    gb->gb_reg.LYC = val;
                    return;

                /* DMA Register */
                case 0x46:
                    gb->gb_reg.DMA = (val % 0xF1);

                    for (uint8_t i = 0; i < OAM_SIZE; i++)
                        gb->oam[i] = __gb_read(gb, (gb->gb_reg.DMA << 8) + i);

                    return;

                /* DMG Palette Registers */
                case 0x47:
                    gb->gb_reg.BGP = val;
                    gb->display.bg_palette[0] = (gb->gb_reg.BGP & 0x03);
                    gb->display.bg_palette[1] = (gb->gb_reg.BGP >> 2) & 0x03;
                    gb->display.bg_palette[2] = (gb->gb_reg.BGP >> 4) & 0x03;
                    gb->display.bg_palette[3] = (gb->gb_reg.BGP >> 6) & 0x03;
                    return;

                case 0x48:
                    gb->gb_reg.OBP0 = val;
                    gb->display.sp_palette[0] = (gb->gb_reg.OBP0 & 0x03);
                    gb->display.sp_palette[1] = (gb->gb_reg.OBP0 >> 2) & 0x03;
                    gb->display.sp_palette[2] = (gb->gb_reg.OBP0 >> 4) & 0x03;
                    gb->display.sp_palette[3] = (gb->gb_reg.OBP0 >> 6) & 0x03;
                    return;

                case 0x49:
                    gb->gb_reg.OBP1 = val;
                    gb->display.sp_palette[4] = (gb->gb_reg.OBP1 & 0x03);
                    gb->display.sp_palette[5] = (gb->gb_reg.OBP1 >> 2) & 0x03;
                    gb->display.sp_palette[6] = (gb->gb_reg.OBP1 >> 4) & 0x03;
                    gb->display.sp_palette[7] = (gb->gb_reg.OBP1 >> 6) & 0x03;
                    return;

                /* Window Position Registers */
                case 0x4A:
                    gb->gb_reg.WY = val;
                    return;

                case 0x4B:
                    gb->gb_reg.WX = val;
                    return;

                /* Prepare Speed Switch*/
                case 0x4D:
                    gb->cgb.doubleSpeedPrep = val & 1;
                    return;

                /* CGB VRAM Bank*/
                case 0x4F:
                    gb->cgb.vramBank = val & 0x01;
                    if (gb->cgb.cgbMode) gb->cgb.vramBankOffset = VRAM_ADDR - (gb->cgb.vramBank << 13);
                    return;

                /* Turn off boot ROM */
                case 0x50:
                    gb->gb_bios_enable = 0;
                    return;

                /* DMA Register */
                case 0x51:
                    gb->cgb.dmaSource = (gb->cgb.dmaSource & 0xFF) + (val << 8);
                    return;
                case 0x52:
                    gb->cgb.dmaSource = (gb->cgb.dmaSource & 0xFF00) + val;
                    return;
                case 0x53:
                    gb->cgb.dmaDest = (gb->cgb.dmaDest & 0xFF) + (val << 8);
                    return;
                case 0x54:
                    gb->cgb.dmaDest = (gb->cgb.dmaDest & 0xFF00) + val;
                    return;

                /* DMA Register*/
                case 0x55:
                    gb->cgb.dmaSize = (val & 0x7F) + 1;
                    gb->cgb.dmaMode = val >> 7;
                    //DMA GBC
                    if (gb->cgb.dmaActive) {  // Only transfer if dma is not active (=1) otherwise treat it as a termination
                        if (gb->cgb.cgbMode && (!gb->cgb.dmaMode)) {
                            for (int i = 0; i < (gb->cgb.dmaSize << 4); i++) {
                                __gb_write(gb, ((gb->cgb.dmaDest & 0x1FF0) | 0x8000) + i, __gb_read(gb, (gb->cgb.dmaSource & 0xFFF0) + i));
                            }
                            gb->cgb.dmaSource += (gb->cgb.dmaSize << 4);
                            gb->cgb.dmaDest += (gb->cgb.dmaSize << 4);
                            gb->cgb.dmaSize = 0;
                        }
                    }
                    gb->cgb.dmaActive = gb->cgb.dmaMode ^ 1;  // set active if it's an HBlank DMA
                    return;

                /* IR Register*/
                case 0x56:
                    gb->hram[0x56] = val;
                    return;

                /* CGB BG Palette Index*/
                case 0x68:
                    gb->cgb.BGPaletteID = val & 0x3F;
                    gb->cgb.BGPaletteInc = val >> 7;
                    return;

                /* CGB BG Palette*/
                case 0x69:
                    gb->cgb.BGPalette[(gb->cgb.BGPaletteID & 0x3F)] = val;
                    fixPaletteTemp = (gb->cgb.BGPalette[(gb->cgb.BGPaletteID & 0x3E) + 1] << 8) + (gb->cgb.BGPalette[(gb->cgb.BGPaletteID & 0x3E)]);
                    gb->cgb.fixPalette[((gb->cgb.BGPaletteID & 0x3E) >> 1)] = ((fixPaletteTemp & 0x7C00) >> 10) | (fixPaletteTemp & 0x03E0) | ((fixPaletteTemp & 0x001F) << 10);  // swap Red and Blue
                    if (gb->cgb.BGPaletteInc) gb->cgb.BGPaletteID = (++gb->cgb.BGPaletteID) & 0x3F;
                    return;

                /* CGB OAM Palette Index*/
                case 0x6A:
                    gb->cgb.OAMPaletteID = val & 0x3F;
                    gb->cgb.OAMPaletteInc = val >> 7;
                    return;

                /* CGB OAM Palette*/
                case 0x6B:
                    gb->cgb.OAMPalette[(gb->cgb.OAMPaletteID & 0x3F)] = val;
                    fixPaletteTemp = (gb->cgb.OAMPalette[(gb->cgb.OAMPaletteID & 0x3E) + 1] << 8) + (gb->cgb.OAMPalette[(gb->cgb.OAMPaletteID & 0x3E)]);
                    gb->cgb.fixPalette[0x20 + ((gb->cgb.OAMPaletteID & 0x3E) >> 1)] = ((fixPaletteTemp & 0x7C00) >> 10) | (fixPaletteTemp & 0x03E0) | ((fixPaletteTemp & 0x001F) << 10);  // swap Red and Blue
                    if (gb->cgb.OAMPaletteInc) gb->cgb.OAMPaletteID = (++gb->cgb.OAMPaletteID) & 0x3F;
                    return;

                /* CGB WRAM Bank*/
                case 0x70:
                    gb->cgb.wramBank = val;
                    gb->cgb.wramBankOffset = WRAM_1_ADDR - (1 << 12);
                    if (gb->cgb.cgbMode && (gb->cgb.wramBank & 7) > 0) gb->cgb.wramBankOffset = WRAM_1_ADDR - ((gb->cgb.wramBank & 7) << 12);
                    return;

                /* Interrupt Enable Register */
                case 0xFF:
                    gb->gb_reg.IE = val;
                    return;
            }
    }

    //(gb->gb_error)(gb, GB_INVALID_WRITE, addr); // ignored
    return;
}

uint8_t __gb_execute_cb(struct gb_s *gb) {
    uint8_t inst_cycles;
    uint8_t cbop = __gb_read(gb, gb->cpu_reg.pc++);
    uint8_t r = (cbop & 0x7);
    uint8_t b = (cbop >> 3) & 0x7;
    uint8_t d = (cbop >> 3) & 0x1;
    uint8_t val;
    uint8_t writeback = 1;

    inst_cycles = 8;
    /* Add an additional 8 cycles to these sets of instructions. */
    switch (cbop & 0xC7) {
        case 0x06:
        case 0x86:
        case 0xC6:
            inst_cycles += 8;
            break;
        case 0x46:
            inst_cycles += 4;
            break;
    }

    switch (r) {
        case 0:
            val = gb->cpu_reg.b;
            break;

        case 1:
            val = gb->cpu_reg.c;
            break;

        case 2:
            val = gb->cpu_reg.d;
            break;

        case 3:
            val = gb->cpu_reg.e;
            break;

        case 4:
            val = gb->cpu_reg.h;
            break;

        case 5:
            val = gb->cpu_reg.l;
            break;

        case 6:
            val = __gb_read(gb, gb->cpu_reg.hl);
            break;

        /* Only values 0-7 are possible here, so we make the final case
     * default to satisfy -Wmaybe-uninitialized warning. */
        default:
            val = gb->cpu_reg.a;
            break;
    }

    /* TODO: Find out WTF this is doing. */
    switch (cbop >> 6) {
        case 0x0:
            cbop = (cbop >> 4) & 0x3;

            switch (cbop) {
                case 0x0:  /* RdC R */
                case 0x1:  /* Rd R */
                    if (d) /* RRC R / RR R */
                    {
                        uint8_t temp = val;
                        val = (val >> 1);
                        val |= cbop ? (gb->cpu_reg.f_bits.c << 7) : (temp << 7);
                        gb->cpu_reg.f_bits.z = (val == 0x00);
                        gb->cpu_reg.f_bits.n = 0;
                        gb->cpu_reg.f_bits.h = 0;
                        gb->cpu_reg.f_bits.c = (temp & 0x01);
                    } else /* RLC R / RL R */
                    {
                        uint8_t temp = val;
                        val = (val << 1);
                        val |= cbop ? gb->cpu_reg.f_bits.c : (temp >> 7);
                        gb->cpu_reg.f_bits.z = (val == 0x00);
                        gb->cpu_reg.f_bits.n = 0;
                        gb->cpu_reg.f_bits.h = 0;
                        gb->cpu_reg.f_bits.c = (temp >> 7);
                    }

                    break;

                case 0x2:
                    if (d) /* SRA R */
                    {
                        gb->cpu_reg.f_bits.c = val & 0x01;
                        val = (val >> 1) | (val & 0x80);
                        gb->cpu_reg.f_bits.z = (val == 0x00);
                        gb->cpu_reg.f_bits.n = 0;
                        gb->cpu_reg.f_bits.h = 0;
                    } else /* SLA R */
                    {
                        gb->cpu_reg.f_bits.c = (val >> 7);
                        val = val << 1;
                        gb->cpu_reg.f_bits.z = (val == 0x00);
                        gb->cpu_reg.f_bits.n = 0;
                        gb->cpu_reg.f_bits.h = 0;
                    }

                    break;

                case 0x3:
                    if (d) /* SRL R */
                    {
                        gb->cpu_reg.f_bits.c = val & 0x01;
                        val = val >> 1;
                        gb->cpu_reg.f_bits.z = (val == 0x00);
                        gb->cpu_reg.f_bits.n = 0;
                        gb->cpu_reg.f_bits.h = 0;
                    } else /* SWAP R */
                    {
                        uint8_t temp = (val >> 4) & 0x0F;
                        temp |= (val << 4) & 0xF0;
                        val = temp;
                        gb->cpu_reg.f_bits.z = (val == 0x00);
                        gb->cpu_reg.f_bits.n = 0;
                        gb->cpu_reg.f_bits.h = 0;
                        gb->cpu_reg.f_bits.c = 0;
                    }

                    break;
            }

            break;

        case 0x1: /* BIT B, R */
            gb->cpu_reg.f_bits.z = !((val >> b) & 0x1);
            gb->cpu_reg.f_bits.n = 0;
            gb->cpu_reg.f_bits.h = 1;
            writeback = 0;
            break;

        case 0x2: /* RES B, R */
            val &= (0xFE << b) | (0xFF >> (8 - b));
            break;

        case 0x3: /* SET B, R */
            val |= (0x1 << b);
            break;
    }

    if (writeback) {
        switch (r) {
            case 0:
                gb->cpu_reg.b = val;
                break;

            case 1:
                gb->cpu_reg.c = val;
                break;

            case 2:
                gb->cpu_reg.d = val;
                break;

            case 3:
                gb->cpu_reg.e = val;
                break;

            case 4:
                gb->cpu_reg.h = val;
                break;

            case 5:
                gb->cpu_reg.l = val;
                break;

            case 6:
                __gb_write(gb, gb->cpu_reg.hl, val);
                break;

            case 7:
                gb->cpu_reg.a = val;
                break;
        }
    }
    return inst_cycles;
}

#if ENABLE_LCD
void __gb_draw_line(struct gb_s *gb) {

    /* If LCD not initialised by front-end, don't render anything. */
    if (gb->display.lcd_draw_line == NULL)
        return;

    if (gb->direct.frame_skip && !gb->display.frame_skip_count)
        return;

    /* If interlaced mode is activated, check if we need to draw the current
    * line. */
    if (gb->direct.interlace) {
        if ((gb->display.interlace_count == 0 && (gb->gb_reg.LY & 1) == 0) || (gb->display.interlace_count == 1 && (gb->gb_reg.LY & 1) == 1)) {
            /* Compensate for missing window draw if required. */
            if (gb->gb_reg.LCDC & LCDC_WINDOW_ENABLE && gb->gb_reg.LY >= gb->display.WY && gb->gb_reg.WX <= 166)
                gb->display.window_clear++;

            return;
        }
    }
    
    if (scanline_sync == 1)
    {
        scanline_sync = 0;
        scanline_count = 0;
        scanline_toggle = 0;
    }
    
    if (scanline_draw == 0)
    {
        /* draw window */
        if (gb->gb_reg.LCDC & LCDC_WINDOW_ENABLE && gb->gb_reg.LY >= gb->display.WY && gb->gb_reg.WX <= 166)
            gb->display.window_clear++;
        
        return;
    }
    
    if (scanline_scaled == 0) scanline_toggle = 0;

    /* If background is enabled, draw it. */
    if (gb->gb_reg.LCDC & LCDC_BG_ENABLE) {
        /* Calculate current background line to draw. Constant because
        * this function draws only this one line each time it is
        * called. */
        const uint8_t bg_y = gb->gb_reg.LY + gb->gb_reg.SCY;

        /* Get selected background map address for first tile
        * corresponding to current line.
        * 0x20 (32) is the width of a background tile, and the bit
        * shift is to calculate the address. */
        const uint16_t bg_map =
            ((gb->gb_reg.LCDC & LCDC_BG_MAP) ? VRAM_BMAP_2 : VRAM_BMAP_1) + (bg_y >> 3) * 0x20;

        /* The displays (what the player sees) X coordinate, drawn right
        * to left. */
        uint8_t disp_x = LCD_WIDTH - 1;

        /* The X coordinate to begin drawing the background at. */
        uint8_t bg_x = disp_x + gb->gb_reg.SCX;

        /* Get tile index for current background tile. */
        uint8_t idx = gb->vram[bg_map + (bg_x >> 3)];
        uint8_t idxAtt = gb->vram[bg_map + (bg_x >> 3) + 0x2000];
        /* Y coordinate of tile pixel to draw. */
        const uint8_t py = (bg_y & 0x07);
        /* X coordinate of tile pixel to draw. */
        uint8_t px = 7 - (bg_x & 0x07);

        uint16_t tile;

        /* Select addressing mode. */
        if (gb->gb_reg.LCDC & LCDC_TILE_SELECT)
            tile = VRAM_TILES_1 + idx * 0x10;
        else
            tile = VRAM_TILES_2 + ((idx + 0x80) % 0x100) * 0x10;

        if (gb->cgb.cgbMode && (idxAtt & 0x08)) tile += 0x2000;  //VRAM bank 2
        if (gb->cgb.cgbMode && (idxAtt & 0x40)) tile += 2 * (7 - py);
        if (!gb->cgb.cgbMode || !(idxAtt & 0x40)) tile += 2 * py;

        /* fetch first tile */
        uint8_t t1, t2;
        if (gb->cgb.cgbMode && (idxAtt & 0x20)) {  //Horizantal Flip
            t1 = gb->vram[tile] << px;
            t2 = gb->vram[tile + 1] << px;
        } else {
            t1 = gb->vram[tile] >> px;
            t2 = gb->vram[tile + 1] >> px;
        }
        for (; disp_x != 0xFF; disp_x--) {
            if (px == 8) {
                /* fetch next tile */
                px = 0;
                bg_x = disp_x + gb->gb_reg.SCX;
                idx = gb->vram[bg_map + (bg_x >> 3)];
                idxAtt = gb->vram[bg_map + (bg_x >> 3) + 0x2000];

                if (gb->gb_reg.LCDC & LCDC_TILE_SELECT)
                    tile = VRAM_TILES_1 + idx * 0x10;
                else
                    tile = VRAM_TILES_2 + ((idx + 0x80) % 0x100) * 0x10;

                if (gb->cgb.cgbMode && (idxAtt & 0x08)) tile += 0x2000;  //VRAM bank 2
                if (gb->cgb.cgbMode && (idxAtt & 0x40)) tile += 2 * (7 - py);
                if (!gb->cgb.cgbMode || !(idxAtt & 0x40)) tile += 2 * py;
                t1 = gb->vram[tile];
                t2 = gb->vram[tile + 1];
            }

            /* copy background */
            if (gb->cgb.cgbMode && (idxAtt & 0x20)) {  //Horizantal Flip
                uint8_t c = (((t1 & 0x80) >> 1) | (t2 & 0x80)) >> 6;
                if (scanline_toggle == 0) scanline_pixels1[disp_x] = ((idxAtt & 0x07) << 2) + c;
                else scanline_pixels2[disp_x] = ((idxAtt & 0x07) << 2) + c;
                scanline_pixels_prio[disp_x] = (idxAtt >> 7);
                t1 = t1 << 1;
                t2 = t2 << 1;
            } else {
                uint8_t c = (t1 & 0x1) | ((t2 & 0x1) << 1);
                if (gb->cgb.cgbMode) {
                    if (scanline_toggle == 0) scanline_pixels1[disp_x] = ((idxAtt & 0x07) << 2) + c;
                    else scanline_pixels2[disp_x] = ((idxAtt & 0x07) << 2) + c;
                    scanline_pixels_prio[disp_x] = (idxAtt >> 7);
                } else {
                    if (scanline_toggle == 0)
                    {
                        scanline_pixels1[disp_x] = gb->display.bg_palette[c];
                        scanline_pixels1[disp_x] |= LCD_PALETTE_BG;
                    }
                    else
                    {
                        scanline_pixels2[disp_x] = gb->display.bg_palette[c];
                        scanline_pixels2[disp_x] |= LCD_PALETTE_BG;
                    }
                }
                t1 = t1 >> 1;
                t2 = t2 >> 1;
            }
            px++;
        }
    }

    /* draw window */
    if (gb->gb_reg.LCDC & LCDC_WINDOW_ENABLE && gb->gb_reg.LY >= gb->display.WY && gb->gb_reg.WX <= 166) {
        /* Calculate Window Map Address. */
        uint16_t win_line = (gb->gb_reg.LCDC & LCDC_WINDOW_MAP) ? VRAM_BMAP_2 : VRAM_BMAP_1;
        win_line += (gb->display.window_clear >> 3) * 0x20;

        uint8_t disp_x = LCD_WIDTH - 1;
        uint8_t win_x = disp_x - gb->gb_reg.WX + 7;

        // look up tile
        uint8_t py = gb->display.window_clear & 0x07;
        uint8_t px = 7 - (win_x & 0x07);
        uint8_t idx = gb->vram[win_line + (win_x >> 3)];
        uint8_t idxAtt = gb->vram[win_line + (win_x >> 3) + 0x2000];
        uint16_t tile;

        if (gb->gb_reg.LCDC & LCDC_TILE_SELECT)
            tile = VRAM_TILES_1 + idx * 0x10;
        else
            tile = VRAM_TILES_2 + ((idx + 0x80) % 0x100) * 0x10;

        if (gb->cgb.cgbMode && (idxAtt & 0x08)) tile += 0x2000;  //VRAM bank 2
        if (gb->cgb.cgbMode && (idxAtt & 0x40)) tile += 2 * (7 - py);
        if (!gb->cgb.cgbMode || !(idxAtt & 0x40)) tile += 2 * py;

        // fetch first tile
        uint8_t t1, t2;
        if (gb->cgb.cgbMode && (idxAtt & 0x20)) {  //Horizantal Flip
            t1 = gb->vram[tile] << px;
            t2 = gb->vram[tile + 1] << px;
        } else {
            t1 = gb->vram[tile] >> px;
            t2 = gb->vram[tile + 1] >> px;
        }
        // loop & copy window
        uint8_t end = (gb->gb_reg.WX < 7 ? 0 : gb->gb_reg.WX - 7) - 1;

        for (; disp_x != end; disp_x--) {
            if (px == 8) {
                // fetch next tile
                px = 0;
                win_x = disp_x - gb->gb_reg.WX + 7;
                idx = gb->vram[win_line + (win_x >> 3)];
                idxAtt = gb->vram[win_line + (win_x >> 3) + 0x2000];

                if (gb->gb_reg.LCDC & LCDC_TILE_SELECT)
                    tile = VRAM_TILES_1 + idx * 0x10;
                else
                    tile = VRAM_TILES_2 + ((idx + 0x80) % 0x100) * 0x10;

                if (gb->cgb.cgbMode && (idxAtt & 0x08)) tile += 0x2000;  //VRAM bank 2
                if (gb->cgb.cgbMode && (idxAtt & 0x40)) tile += 2 * (7 - py);
                if (!gb->cgb.cgbMode || !(idxAtt & 0x40)) tile += 2 * py;
                t1 = gb->vram[tile];
                t2 = gb->vram[tile + 1];
            }

            // copy window
            if (idxAtt & 0x20) {  //Horizantal Flip
                uint8_t c = (((t1 & 0x80) >> 1) | (t2 & 0x80)) >> 6;
                if (scanline_toggle == 0) scanline_pixels1[disp_x] = ((idxAtt & 0x07) << 2) + c;
                else scanline_pixels2[disp_x] = ((idxAtt & 0x07) << 2) + c;
                scanline_pixels_prio[disp_x] = (idxAtt >> 7);
                t1 = t1 << 1;
                t2 = t2 << 1;
            } else {
                uint8_t c = (t1 & 0x1) | ((t2 & 0x1) << 1);
                if (gb->cgb.cgbMode) {
                    if (scanline_toggle == 0) scanline_pixels1[disp_x] = ((idxAtt & 0x07) << 2) + c;
                    else scanline_pixels2[disp_x] = ((idxAtt & 0x07) << 2) + c;
                    scanline_pixels_prio[disp_x] = (idxAtt >> 7);
                } else {
                    if (scanline_toggle == 0)
                    {
                        scanline_pixels1[disp_x] = gb->display.bg_palette[c];
                        scanline_pixels1[disp_x] |= LCD_PALETTE_BG;
                    }
                    else
                    {  
                        scanline_pixels2[disp_x] = gb->display.bg_palette[c];
                        scanline_pixels2[disp_x] |= LCD_PALETTE_BG;
                    }
                }
                t1 = t1 >> 1;
                t2 = t2 >> 1;
            }
            px++;
        }

        gb->display.window_clear++;  // advance window line
    }

    // draw sprites
    if (gb->gb_reg.LCDC & LCDC_OBJ_ENABLE) {
        uint8_t count = 0;

        for (uint8_t s = NUM_SPRITES - 1;
             s != 0xFF /* && count < MAX_SPRITES_LINE */;
             s--) {
            /* Sprite Y position. */
            uint8_t OY = gb->oam[4 * s + 0];
            /* Sprite X position. */
            uint8_t OX = gb->oam[4 * s + 1];
            /* Sprite Tile/Pattern Number. */
            uint8_t OT = gb->oam[4 * s + 2] & (gb->gb_reg.LCDC & LCDC_OBJ_SIZE ? 0xFE : 0xFF);
            /* Additional attributes. */
            uint8_t OF = gb->oam[4 * s + 3];

            /* If sprite isn't on this line, continue. */
            if (gb->gb_reg.LY +
                        (gb->gb_reg.LCDC & LCDC_OBJ_SIZE ? 0 : 8) >=
                    OY ||
                gb->gb_reg.LY + 16 < OY)
                continue;

            count++;

            /* Continue if sprite not visible. */
            if (OX == 0 || OX >= 168)
                continue;

            // y flip
            uint8_t py = gb->gb_reg.LY - OY + 16;

            if (OF & OBJ_FLIP_Y)
                py = (gb->gb_reg.LCDC & LCDC_OBJ_SIZE ? 15 : 7) - py;

            // fetch the tile
            uint8_t t1, t2;
            if (gb->cgb.cgbMode) {
                t1 = gb->vram[((OF & OBJ_BANK) << 10) + VRAM_TILES_1 + OT * 0x10 + 2 * py];
                t2 = gb->vram[((OF & OBJ_BANK) << 10) + VRAM_TILES_1 + OT * 0x10 + 2 * py + 1];
            } else {
                t1 = gb->vram[VRAM_TILES_1 + OT * 0x10 + 2 * py];
                t2 = gb->vram[VRAM_TILES_1 + OT * 0x10 + 2 * py + 1];
            }

            // handle x flip
            uint8_t dir, start, end, shift;

            if (OF & OBJ_FLIP_X) {
                dir = 1;
                start = (OX < 8 ? 0 : OX - 8);
                end = MIN(OX, LCD_WIDTH);
                shift = 8 - OX + start;
            } else {
                dir = -1;
                start = MIN(OX, LCD_WIDTH) - 1;
                end = (OX < 8 ? 0 : OX - 8) - 1;
                shift = OX - (start + 1);
            }

            // copy tile
            t1 >>= shift;
            t2 >>= shift;

            for (uint8_t disp_x = start; disp_x != end; disp_x += dir) {
                 
                uint8_t c = (t1 & 0x1) | ((t2 & 0x1) << 1);
                // check transparency / sprite overlap / background overlap
                if (scanline_toggle == 0)
                {
                    if (gb->cgb.cgbMode && (c && !(scanline_pixels_prio[disp_x] && (scanline_pixels1[disp_x] & 0x3)) && 
                        !((OF & OBJ_PRIORITY) && (scanline_pixels1[disp_x] & 0x3)))) {
                        /* Set pixel colour. */
                        scanline_pixels1[disp_x] = ((OF & OBJ_CGB_PALETTE) << 2) + c + 0x20;  // add 0x20 to differentiate from BG
                    } else if (c && !(OF & OBJ_PRIORITY && scanline_pixels1[disp_x] & 0x3)) {
                        
                        if (gb->cgb.cgbMode && scanline_hack > 0)
                        {
                            // THIS IS A HACK! IT WORKS FOR ZELDA GBC GAMES!
                        }
                        else
                        {
                            /* Set pixel colour. */
                            scanline_pixels1[disp_x] = (OF & OBJ_PALETTE)
                                                 ? gb->display.sp_palette[c + 4]
                                                 : gb->display.sp_palette[c];
                            /* Set pixel palette (OBJ0 or OBJ1). */
                            scanline_pixels1[disp_x] |= (OF & OBJ_PALETTE);
                            /* Deselect BG palette. */
                            scanline_pixels1[disp_x] &= ~LCD_PALETTE_BG;
                        }
                    }
                }
                else
                {
                    if (gb->cgb.cgbMode && (c && !(scanline_pixels_prio[disp_x] && (scanline_pixels2[disp_x] & 0x3)) && 
                        !((OF & OBJ_PRIORITY) && (scanline_pixels2[disp_x] & 0x3)))) {
                        /* Set pixel colour. */
                        scanline_pixels2[disp_x] = ((OF & OBJ_CGB_PALETTE) << 2) + c + 0x20;  // add 0x20 to differentiate from BG
                    } else if (c && !(OF & OBJ_PRIORITY && scanline_pixels2[disp_x] & 0x3)) {
                        
                        if (gb->cgb.cgbMode && scanline_hack > 0)
                        {
                            // THIS IS A HACK! IT WORKS FOR ZELDA GBC GAMES!
                        }
                        else
                        {
                            /* Set pixel colour. */
                            scanline_pixels2[disp_x] = (OF & OBJ_PALETTE)
                                                 ? gb->display.sp_palette[c + 4]
                                                 : gb->display.sp_palette[c];
                            /* Set pixel palette (OBJ0 or OBJ1). */
                            scanline_pixels2[disp_x] |= (OF & OBJ_PALETTE);
                            /* Deselect BG palette. */
                            scanline_pixels2[disp_x] &= ~LCD_PALETTE_BG;
                        }
                    }
                }

                t1 = t1 >> 1;
                t2 = t2 >> 1;
            }
        }
    }

    if (scanline_toggle == 0)
    {
        if (scanline_scaled == 0)
        {
            gb->display.lcd_draw_line(gb,
                //scanline_pixels1,
                //scanline_pixels2,
                gb->gb_reg.LY
            );
        }
        else
        {
            scanline_toggle = 1;
        }
    }
    else
    {
        scanline_toggle = 0;
        
        gb->display.lcd_draw_line(gb,
            //scanline_pixels1,
            //scanline_pixels2,
            gb->gb_reg.LY
        );
        
        scanline_count += 3;
    }
}
#endif
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
